ArribasRaul/Cargador-solar-de-baterias-para-nodos-IoT/1. Codigos/Sistema_de_medida/Montaje 5V.jpg

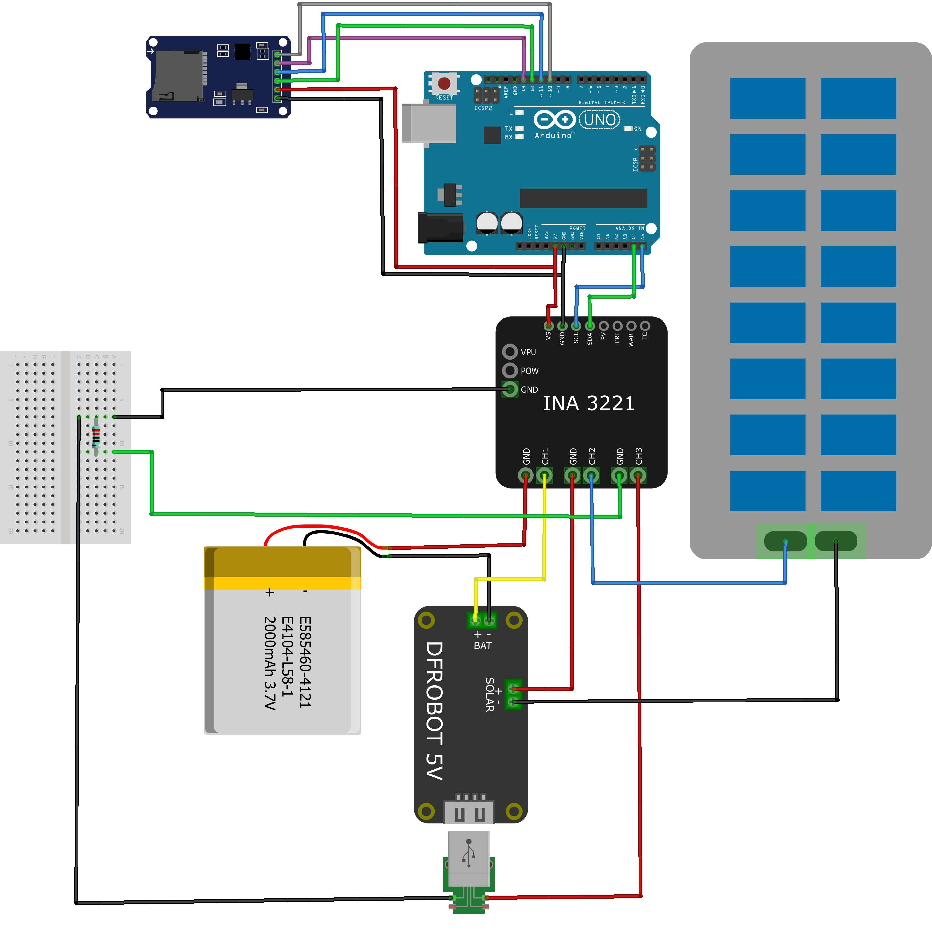
1. Codigos/Sistema_de_medida/Montaje 5V.jpg
