ArribasRaul/Cargador-solar-de-baterias-para-nodos-IoT/2. PCB/Fotos PCB/2. Top solder masck.png

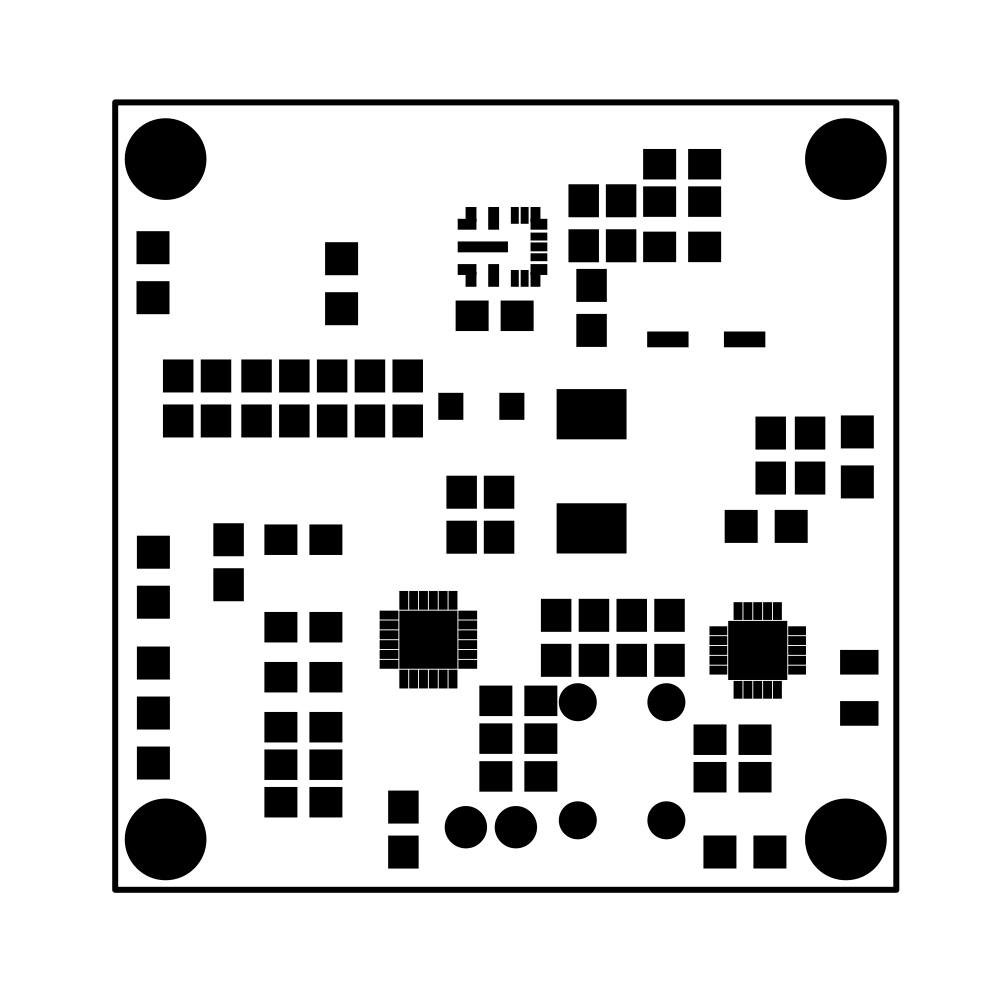
2. PCB/Fotos PCB/2. Top solder masck.png
