ArribasRaul/Cargador-solar-de-baterias-para-nodos-IoT/2. PCB/Fotos PCB/5. Botton solder mask.png

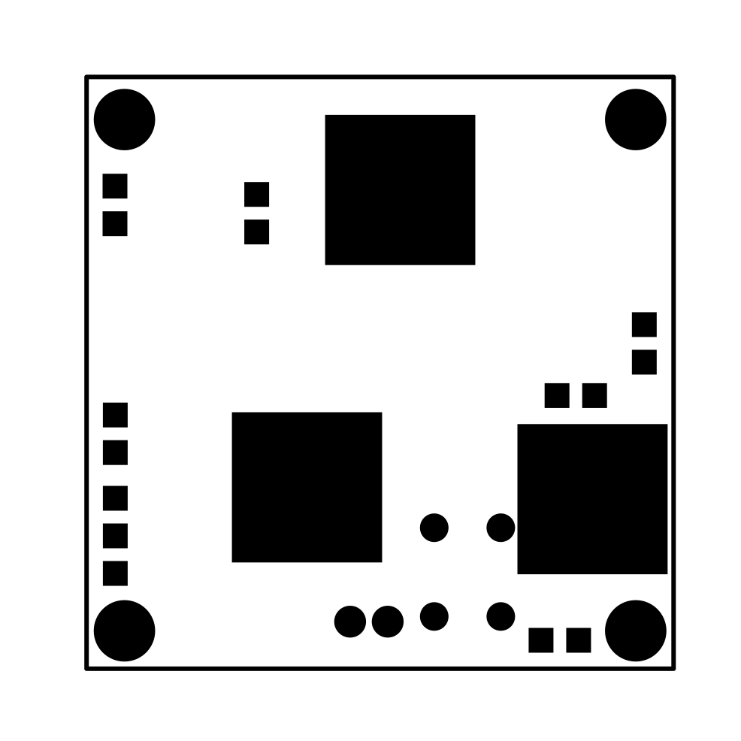
2. PCB/Fotos PCB/5. Botton solder mask.png
